Xinyuan-LilyGO/LilyGO-T-SIM7000G/docs/SIM7070/SIM7070G_CTA证书_2021.pdf

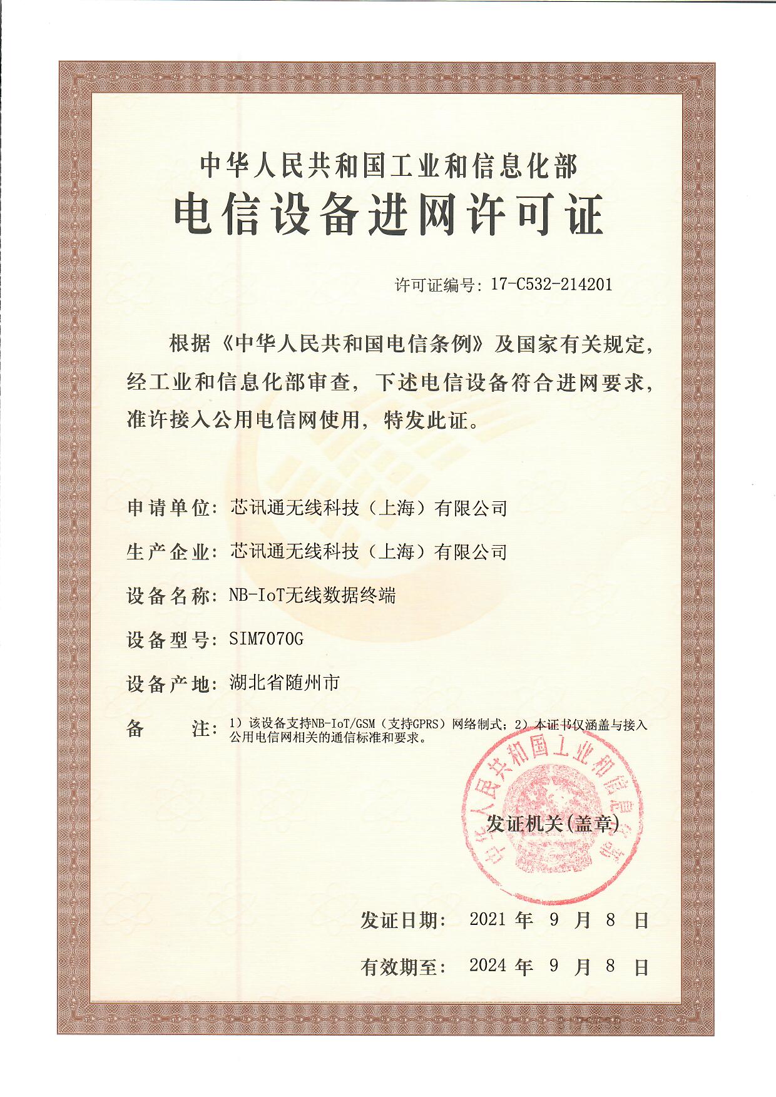
[picture p25: page 1]
