Xinyuan-LilyGO/LilyGO-T-SIM7000G/docs/SIM7070/SIM7070G_NCC_证书_2020.pdf

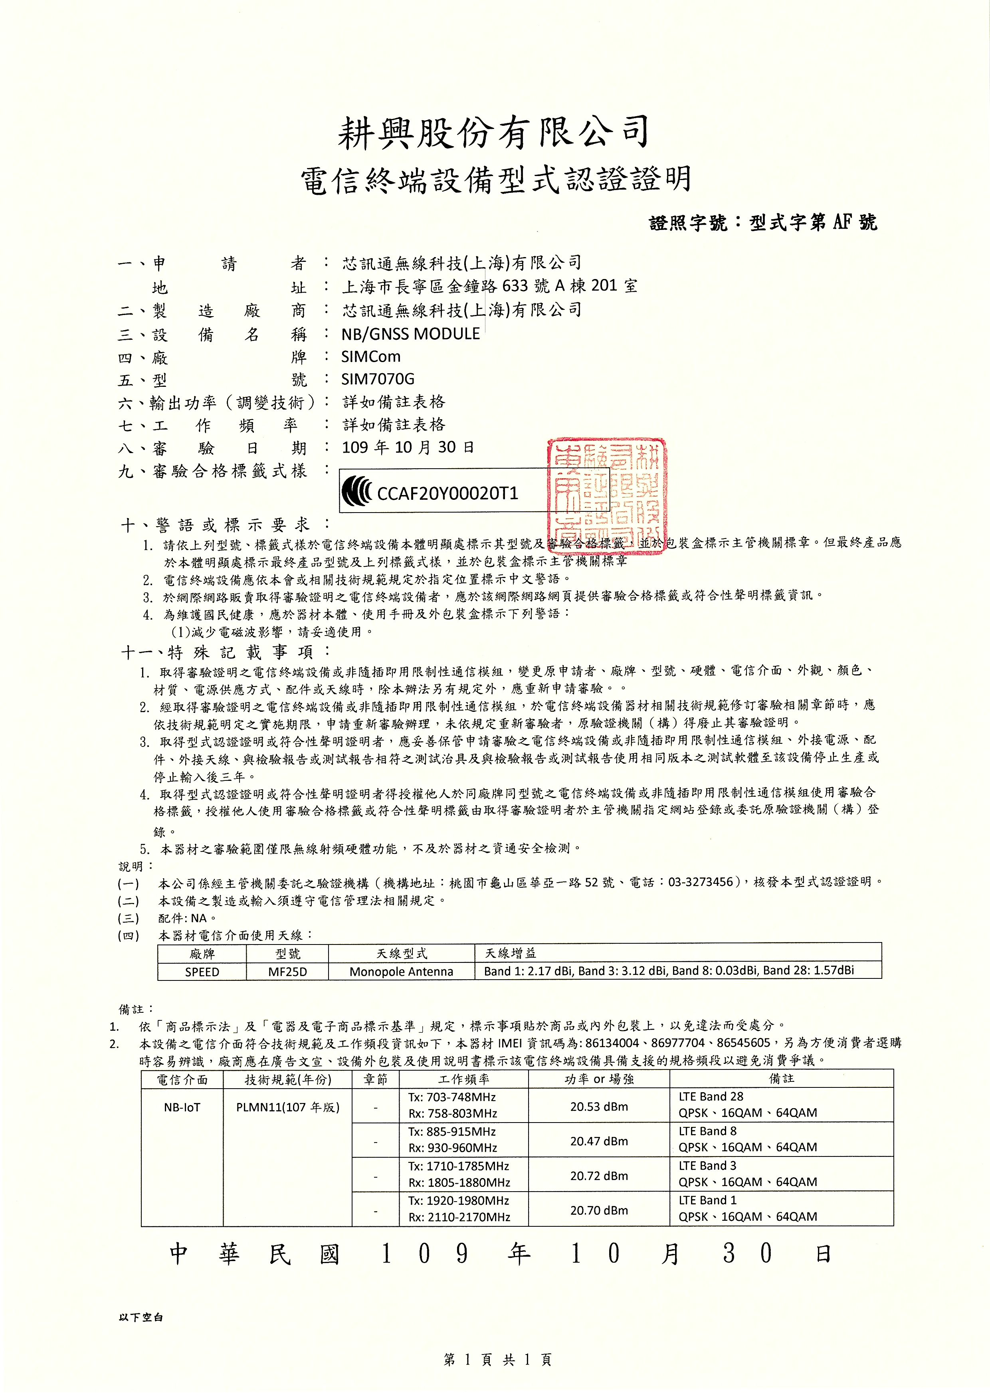
[picture p26: page 1]
