Xinyuan-LilyGO/LilyGO-T-SIM7000G/Historical/Image/externalDownloader.jpg

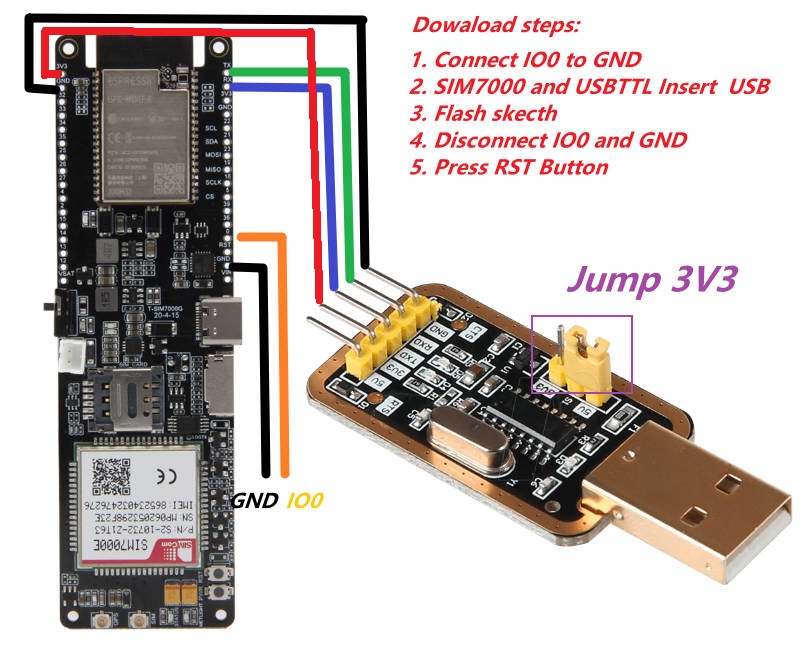
Historical/Image/externalDownloader.jpg
