Xinyuan-LilyGO/LilyGO-T-SIM7000G/image/CBANDCFG.png

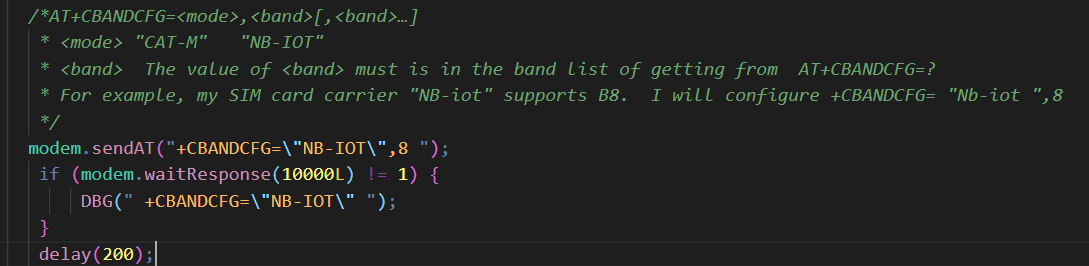
image/CBANDCFG.png
