Xinyuan-LilyGO/LilyGO-T-SIM7000G/image/LTE.png

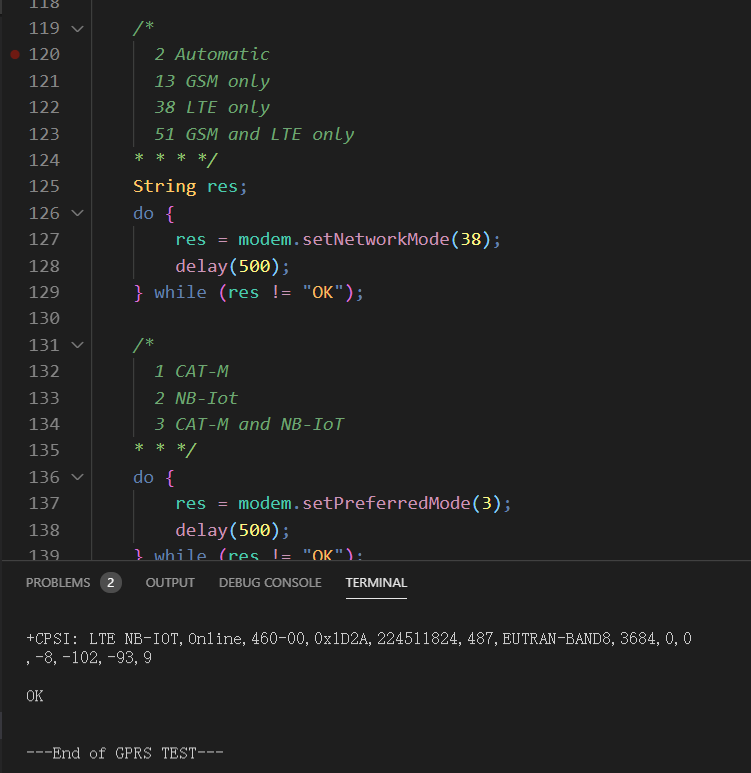
image/LTE.png
