Xinyuan-LilyGO/LilyGO-T-SIM7000G/examples/Arduino_Cayenne/LilyGO-SIM7000-Cayenne.ino

#define TINY_GSM_DEBUG Serial
#define CAYENNE_PRINT Serial
#define TINY_GSM_MODEM_SIM7000


#define USE_GSM  //! Uncomment will use SIM7000 for GSM communication

#ifdef USE_GSM
#include <CayenneMQTTGSM.h>
#else
#include <CayenneMQTTESP32.h>
#endif
#include <Arduino.h>
#include <Wire.h>
#include <Adafruit_BMP085.h>


#define TEMPERATURE_VIRTUAL_CHANNEL         1
#define BAROMETER_VIRTUAL_CHANNEL           2
#define ALTITUDE_VIRTUAL_CHANNEL            3
#define BATTERY_VIRTUAL_CHANNEL             4
#define SOLAR_VIRTUAL_CHANNEL               5
#define LIGHTSENSOR_VIRTUAL_CHANNEL         6

#define PIN_TX      27
#define PIN_RX      26
#define UART_BAUD   115200
#define PWR_PIN     4
#define BAT_ADC     35
#define SOLAR_ADC   36

Adafruit_BMP085 bmp;
HardwareSerial  gsmSerial(1);

#ifdef USE_GSM
// GSM connection info.
char apn[] = ""; // Access point name. Leave empty if it is not needed.
char gprsLogin[] = ""; // GPRS username. Leave empty if it is not needed.
char gprsPassword[] = ""; // GPRS password. Leave empty if it is not needed.
char pin[] = ""; // SIM pin number. Leave empty if it is not needed.
#else
// WiFi network info.
char ssid[] = "your wifi ssid";
char wifiPassword[] = "your wifi password";
#endif

// Cayenne authentication info. This should be obtained from the Cayenne Dashboard.
char username[] = "Cayenne username";
char password[] = "Cayenne password";
char clientID[] = "Cayenne clientID";

bool bmpSensorDetected = true;



void setup()
{
    Serial.begin(UART_BAUD);
    gsmSerial.begin(UART_BAUD, SERIAL_8N1, PIN_RX, PIN_TX);

    pinMode(PWR_PIN, OUTPUT);

    //Launch SIM7000
    digitalWrite(PWR_PIN, HIGH);
    // Starting the machine requires at least 1 second of low level, and with a level conversion, the levels are opposite
    delay(1000);
    digitalWrite(PWR_PIN, LOW);


    // Launch BMP085
    if (!bmp.begin()) {
        bmpSensorDetected = false;
        Serial.println("Could not find a valid BMP085 sensor, check wiring!");
        while (1) {}
    }

    //Wait for the SIM7000 communication to be normal, and will quit when receiving any byte
    int i = 6;
    delay(200);
    while (i) {
        Serial.println("Send AT");
        gsmSerial.println("AT");
        if (gsmSerial.available()) {
            String r = gsmSerial.readString();
            Serial.println(r);
            break;
        }
        delay(1000);
        i--;
    }

#ifdef USE_GSM
    Cayenne.begin(username, password, clientID, gsmSerial, apn, gprsLogin, gprsPassword, pin);
#else
    Cayenne.begin(username, password, clientID, ssid, wifiPassword);
#endif
}


void loop()
{
    Cayenne.loop();
}




// Default function for processing actuator commands from the Cayenne Dashboard.
// You can also use functions for specific channels, e.g CAYENNE_IN(1) for channel 1 commands.
CAYENNE_IN_DEFAULT()
{
    CAYENNE_LOG("Channel %u, value %s", request.channel, getValue.asString());
    //Process message here. If there is an error set an error message using getValue.setError(), e.g getValue.setError("Error message");
}

CAYENNE_IN(1)
{
    CAYENNE_LOG("Channel %u, value %s", request.channel, getValue.asString());
}


// This function is called at intervals to send temperature sensor data to Cayenne.
CAYENNE_OUT(TEMPERATURE_VIRTUAL_CHANNEL)
{

    if (bmpSensorDetected) {
        float temperature = bmp.readTemperature();

        Serial.print("Temperature = ");
        Serial.print(temperature);
        Serial.println(" *C");

        Cayenne.celsiusWrite(TEMPERATURE_VIRTUAL_CHANNEL, temperature);
    }
}

// This function is called at intervals to send barometer sensor data to Cayenne.
CAYENNE_OUT(BAROMETER_VIRTUAL_CHANNEL)
{
    if (bmpSensorDetected) {
        float pressure = bmp.readPressure() / 1000;

        Serial.print("Pressure = ");
        Serial.print(pressure );
        Serial.println(" hPa");

        Cayenne.hectoPascalWrite(BAROMETER_VIRTUAL_CHANNEL, pressure);
    }
}


CAYENNE_OUT(ALTITUDE_VIRTUAL_CHANNEL)
{
    if (bmpSensorDetected) {
        float altitude = bmp.readAltitude();

        Serial.print("Altitude = ");
        Serial.print(altitude);
        Serial.println(" meters");

        Cayenne.virtualWrite(ALTITUDE_VIRTUAL_CHANNEL, altitude, "meters", UNIT_METER);

    }
}

float readBattery(uint8_t pin)
{
    int vref = 1100;
    uint16_t volt = analogRead(pin);
    float battery_voltage = ((float)volt / 4095.0) * 2.0 * 3.3 * (vref);
    return battery_voltage;
}


CAYENNE_OUT(BATTERY_VIRTUAL_CHANNEL)
{
    float mv = readBattery(BAT_ADC);
    Serial.printf("batter : %f\n", mv);
    Cayenne.virtualWrite(BATTERY_VIRTUAL_CHANNEL, mv, TYPE_VOLTAGE, UNIT_MILLIVOLTS);

}


CAYENNE_OUT(SOLAR_VIRTUAL_CHANNEL)
{
    float mv = readBattery(SOLAR_ADC);
    Serial.printf("solar : %f\n", mv);
    Cayenne.virtualWrite(SOLAR_VIRTUAL_CHANNEL, mv, TYPE_VOLTAGE, UNIT_MILLIVOLTS);

}
